KarlZeilhofer/htl-loetregler-mini/3d/batterie-adapter/bosch-hobby-18v/images/1d0ade216039de442b552e4a9faad1e7_preview_featured.JPG

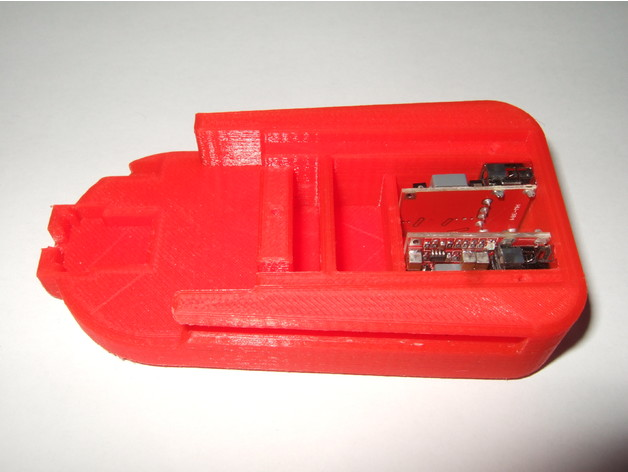
3d/batterie-adapter/bosch-hobby-18v/images/1d0ade216039de442b552e4a9faad1e7_preview_featured.JPG
