KarlZeilhofer/htl-loetregler-mini/3d/batterie-adapter/bosch-hobby-18v/images/18e0baede5127a3ce2cf0de32edce1c3_preview_featured.jpg

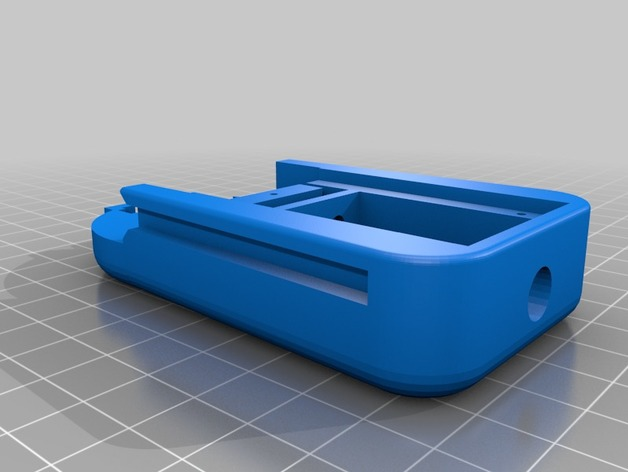
3d/batterie-adapter/bosch-hobby-18v/images/18e0baede5127a3ce2cf0de32edce1c3_preview_featured.jpg
