KarlZeilhofer/htl-loetregler-mini/3d/batterie-adapter/bosch-hobby-18v/images/176e3c1223d7b4e42e6c2fdfab14404a_preview_featured.JPG

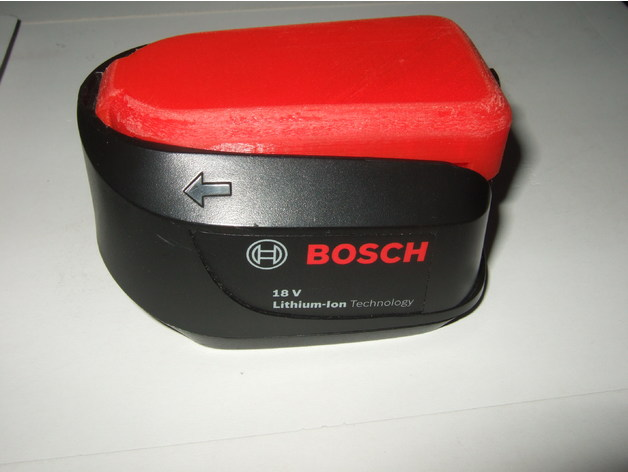
3d/batterie-adapter/bosch-hobby-18v/images/176e3c1223d7b4e42e6c2fdfab14404a_preview_featured.JPG
