KarlZeilhofer/htl-loetregler-mini/3d/batterie-adapter/bosch-hobby-18v/images/217fe692acae399ae9cad3a89807bee1_preview_featured.JPG

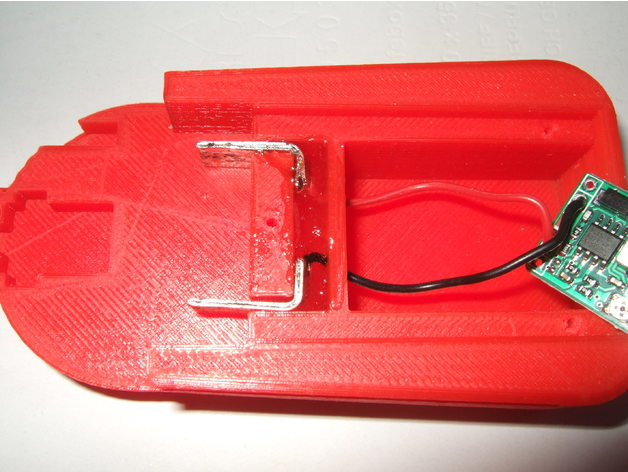
3d/batterie-adapter/bosch-hobby-18v/images/217fe692acae399ae9cad3a89807bee1_preview_featured.JPG
