KarlZeilhofer/htl-loetregler-mini/3d/batterie-adapter/bosch-hobby-18v/images/428f00f09416d94f13bab7031078e59d_preview_featured.JPG

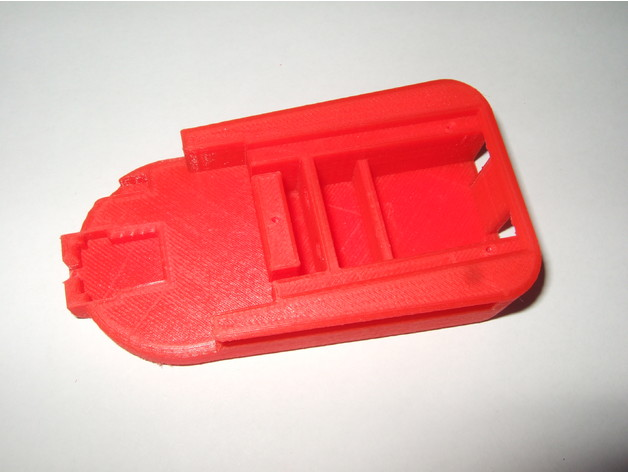
3d/batterie-adapter/bosch-hobby-18v/images/428f00f09416d94f13bab7031078e59d_preview_featured.JPG
