KarlZeilhofer/htl-loetregler-mini/3d/batterie-adapter/bosch-hobby-18v/images/aad29fb0102c40d275100bae19a4c0d0_preview_featured.JPG

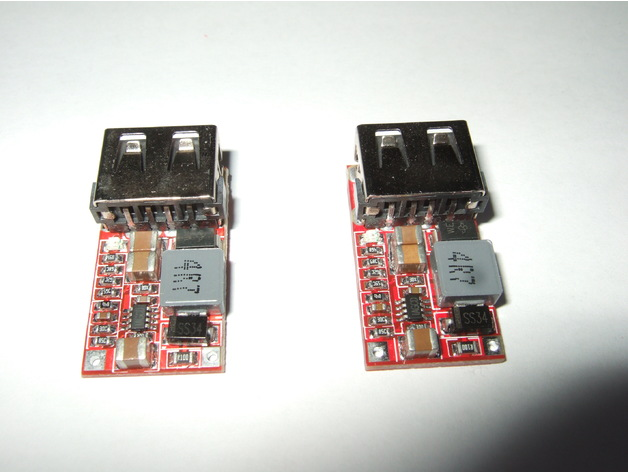
3d/batterie-adapter/bosch-hobby-18v/images/aad29fb0102c40d275100bae19a4c0d0_preview_featured.JPG
