KarlZeilhofer/htl-loetregler-mini/3d/batterie-adapter/bosch-hobby-18v/images/c5ce1f0b2175b3c10ee5914f01ce9187_preview_featured.JPG

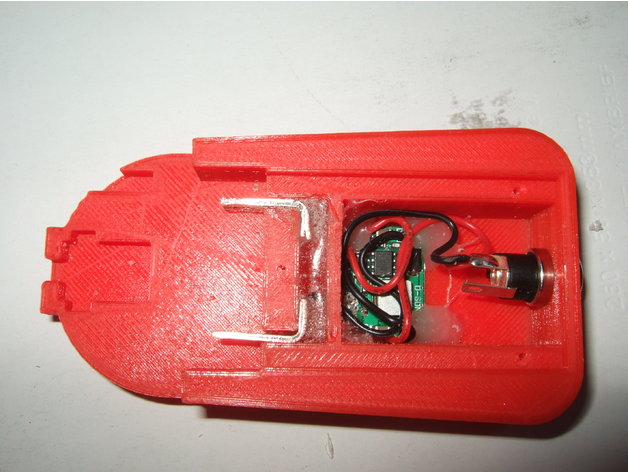
3d/batterie-adapter/bosch-hobby-18v/images/c5ce1f0b2175b3c10ee5914f01ce9187_preview_featured.JPG
