KarlZeilhofer/htl-loetregler-mini/3d/batterie-adapter/einhell/2022-06-26_001.png

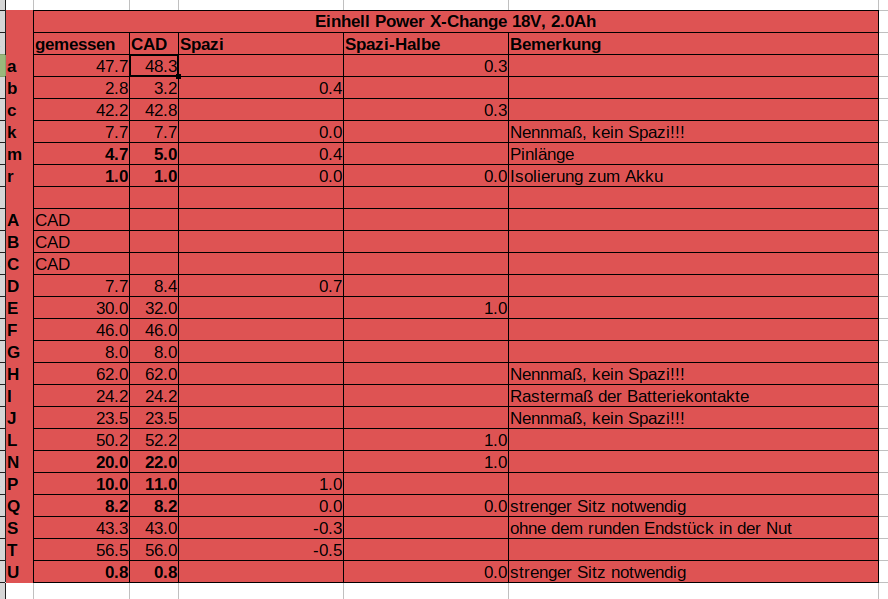
3d/batterie-adapter/einhell/2022-06-26_001.png
