KarlZeilhofer/htl-loetregler-mini/3d/batterie-adapter/einhell/skizze-aufriss.jpg

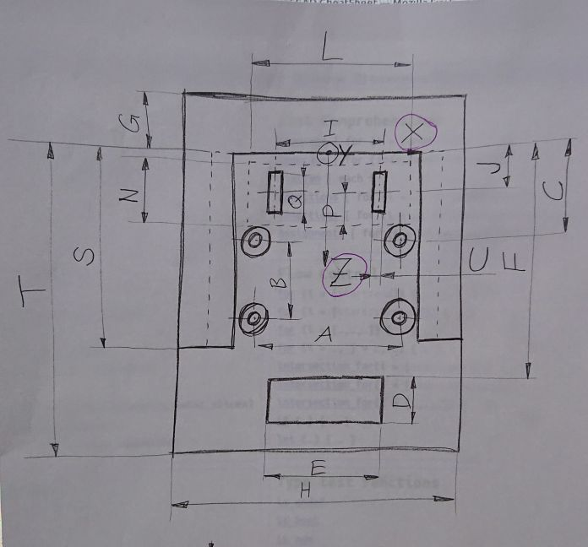
3d/batterie-adapter/einhell/skizze-aufriss.jpg
