KarlZeilhofer/htl-loetregler-mini/3d/batterie-adapter/einhell/skizze-grundriss.jpg

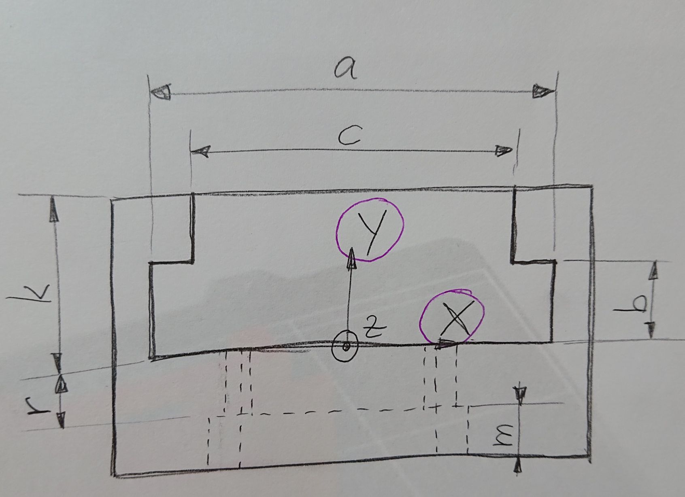
3d/batterie-adapter/einhell/skizze-grundriss.jpg
