KarlZeilhofer/htl-loetregler-mini/3d/batterie-adapter/lux-tools-1.5ah/LUX Tools 20V-1.5Ah.jpg

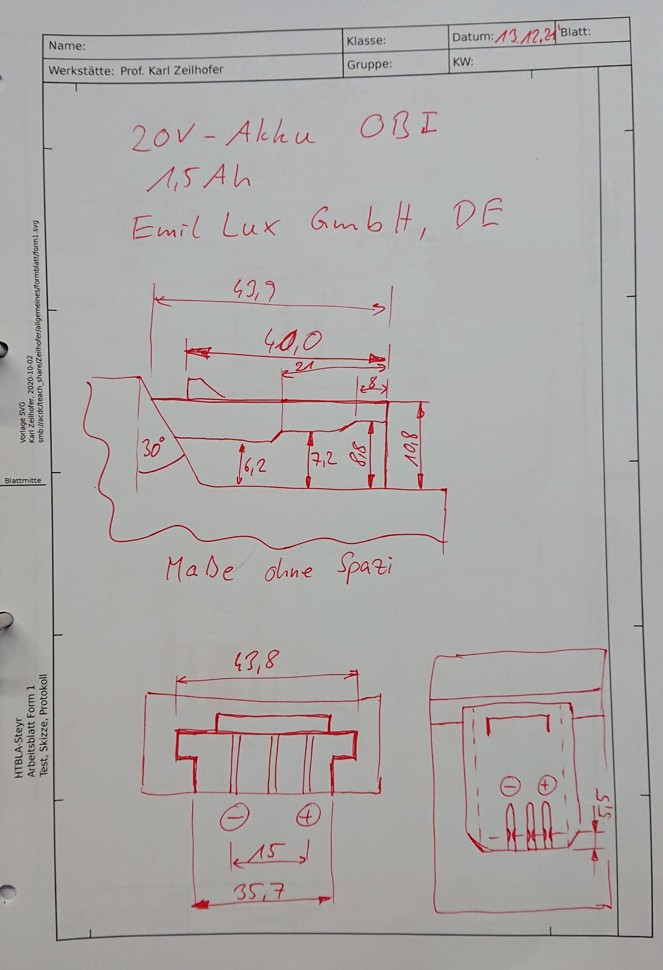
3d/batterie-adapter/lux-tools-1.5ah/LUX Tools 20V-1.5Ah.jpg
