KarlZeilhofer/htl-loetregler-mini/3d/batterie-adapter/lux-tools-2ah/LUX Tools 20V-2Ah.jpg

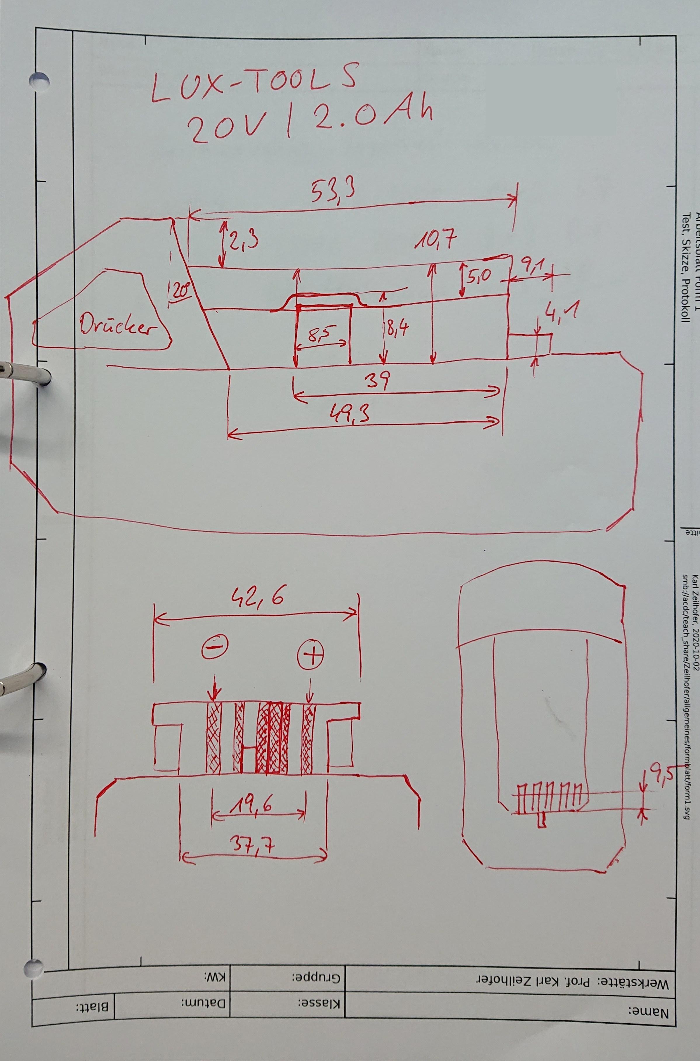
3d/batterie-adapter/lux-tools-2ah/LUX Tools 20V-2Ah.jpg
