KarlZeilhofer/htl-loetregler-mini/3d/griffstük/screenshot griffstück v1.png

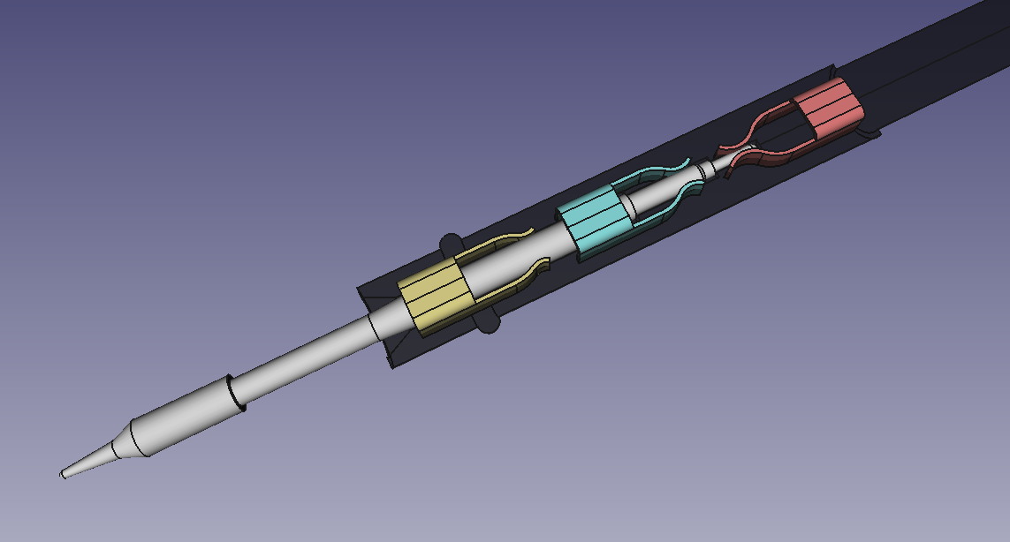
3d/griffstük/screenshot griffstück v1.png
