KarlZeilhofer/htl-loetregler-mini/berechnungen/spannungen_leistungen_spitzentypen.png

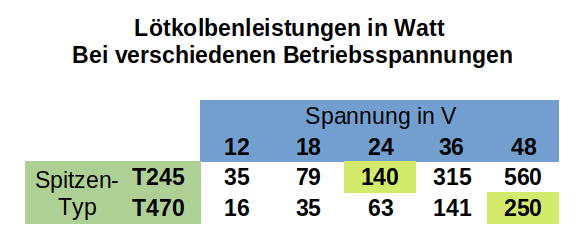
berechnungen/spannungen_leistungen_spitzentypen.png
