KarlZeilhofer/htl-loetregler-mini/kicad/cam/untitled.png

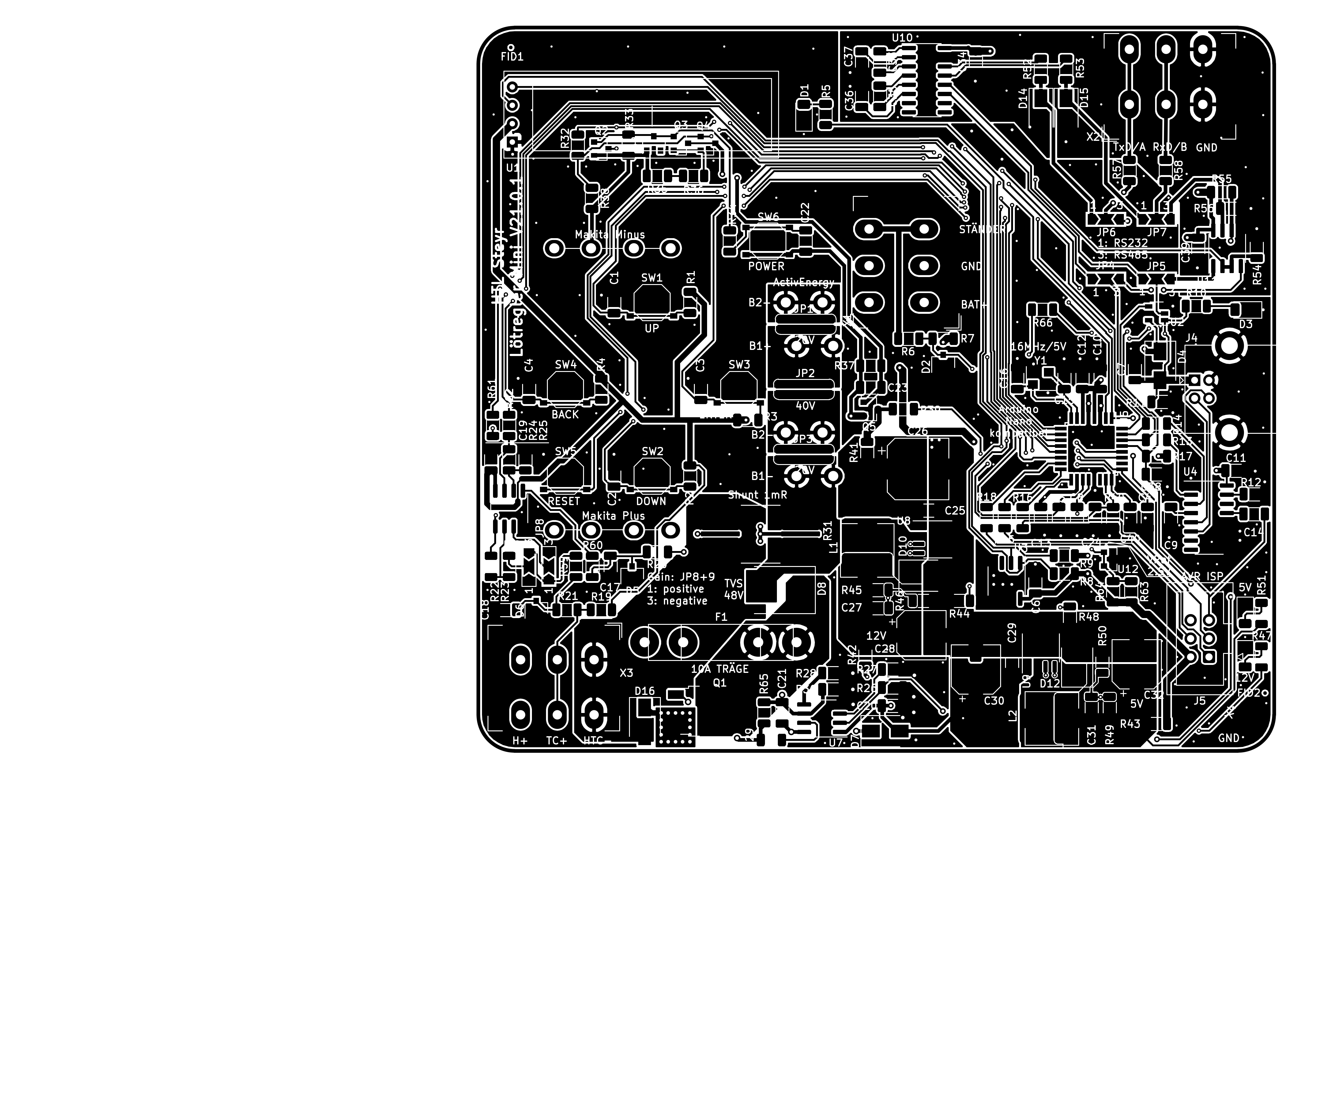
kicad/cam/untitled.png
