KarlZeilhofer/htl-loetregler-mini/3d/batterie-adapter/lux-tools-1.5ah/LUX Tools 20V-1.5Ah, Deckel v1.stl

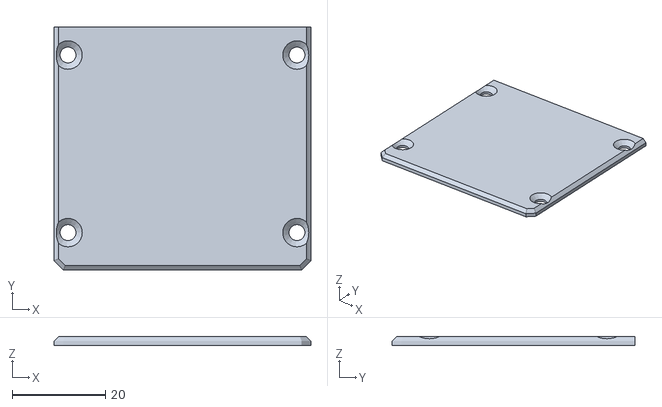
[picture p37: CAD file, 2022-02-06]
3d/batterie-adapter/lux-tools-1.5ah/LUX Tools 20V-1.5Ah, Deckel v1.stl
55.0 x 52.0 x 2.00
