KarlZeilhofer/htl-loetregler-mini/3d/batterie-adapter/milwaukee/milwaukee-batterieschuh_v2.stl

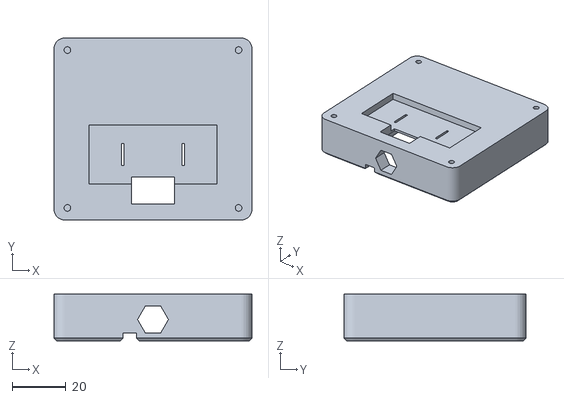
[picture p38: CAD file, 2022-06-27]
3d/batterie-adapter/milwaukee/milwaukee-batterieschuh_v2.stl
74.0 x 68.0 x 17.5
