KarlZeilhofer/htl-loetregler-mini/3d/griffstük/fingerkuppenring_v2.3.stl

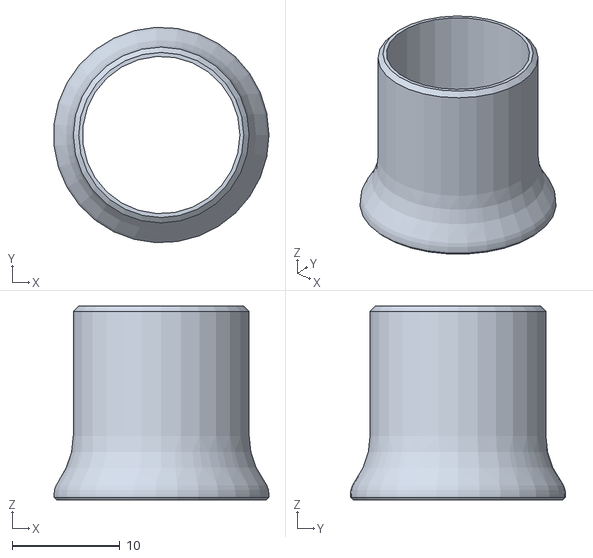
[picture p39: CAD file, 2022-06-27]
3d/griffstük/fingerkuppenring_v2.3.stl
19.9 x 20.0 x 18.0
