KarlZeilhofer/htl-loetregler-mini/3d/tiefziehform/tiefziehform_A_matrizze_v3.stl

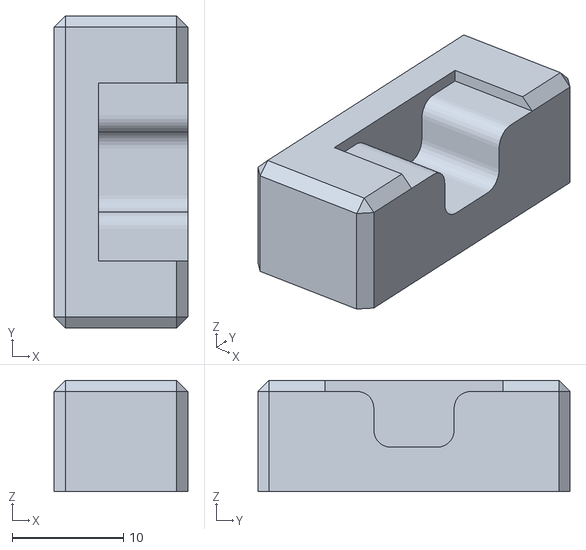
[picture p40: CAD file, 2021-06-21]
3d/tiefziehform/tiefziehform_A_matrizze_v3.stl
12.0 x 28.0 x 10.0
