KarlZeilhofer/htl-loetregler-mini/3d/batterie-adapter/berner-18v/berner-batterieschuh.FCStd

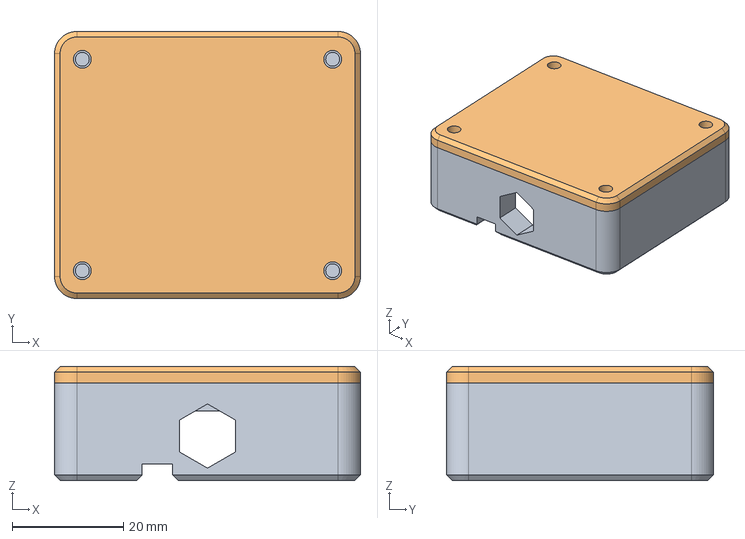
[picture p41: CAD file, 2021-11-27]
3d/batterie-adapter/berner-18v/berner-batterieschuh.FCStd
55.0 x 48.0 x 20.5 mm
Berner-18V
Deckel
