KarlZeilhofer/htl-loetregler-mini/3d/batterie-adapter/bosch-hobby-18v/files/deckel.stl

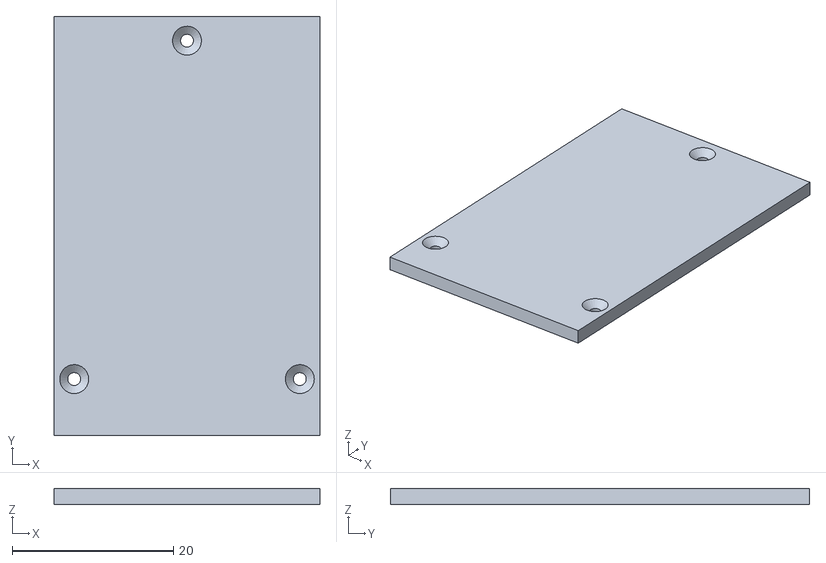
[picture p42: CAD file, 2022-02-07]
3d/batterie-adapter/bosch-hobby-18v/files/deckel.stl
33.0 x 52.0 x 2.00
