KarlZeilhofer/htl-loetregler-mini/3d/batterie-adapter/bosch-professional-18v/bosch-professional-batterieschuh_deckel_v1.stl

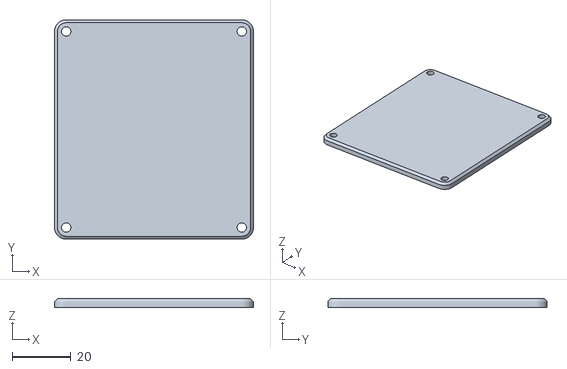
[picture p43: CAD file, 2022-06-01]
3d/batterie-adapter/bosch-professional-18v/bosch-professional-batterieschuh_deckel_v1.stl
68.0 x 75.0 x 3.00
