KarlZeilhofer/htl-loetregler-mini/3d/batterie-adapter/lux-tools-1.5ah/LUX Tools 20V-1.5Ah, Schuh v1.stl

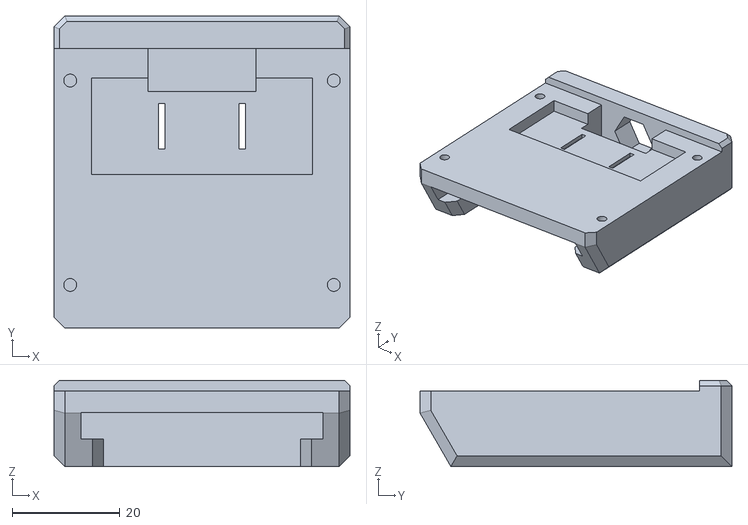
[picture p44: CAD file, 2022-02-06]
3d/batterie-adapter/lux-tools-1.5ah/LUX Tools 20V-1.5Ah, Schuh v1.stl
55.0 x 58.0 x 16.0
