KarlZeilhofer/htl-loetregler-mini/3d/batterie-adapter/lux-tools-2ah/lux-tools-2Ah_batterieschuh_deckel_v2.stl

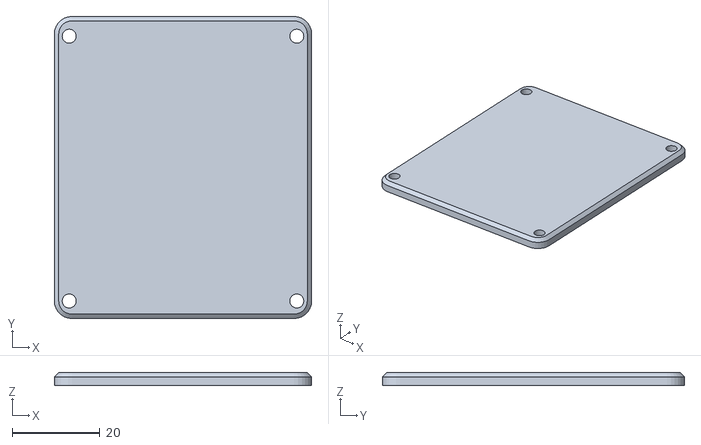
[picture p45: CAD file, 2022-06-27]
3d/batterie-adapter/lux-tools-2ah/lux-tools-2Ah_batterieschuh_deckel_v2.stl
58.8 x 69.0 x 3.00
