KarlZeilhofer/htl-loetregler-mini/3d/gehäuse/lötregler-gehäuse.FCStd

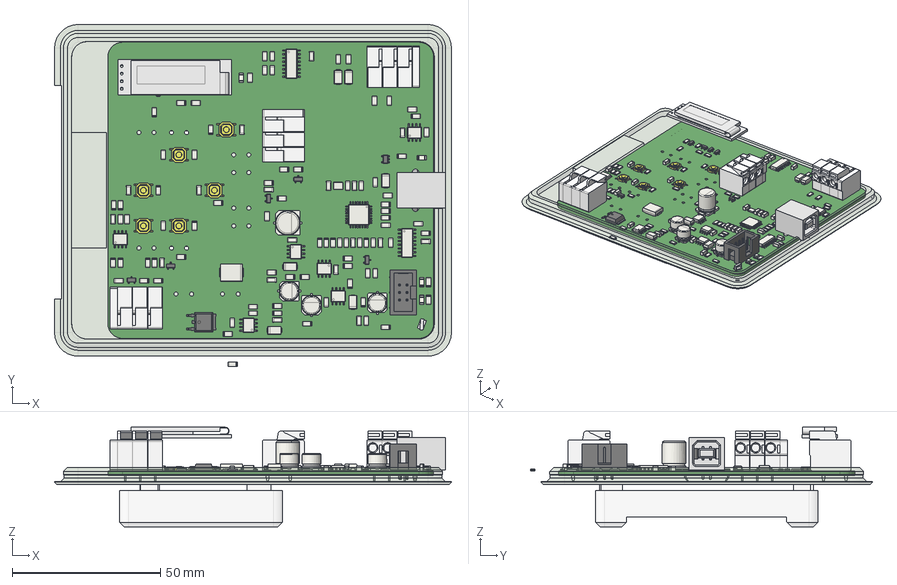
[picture p46: CAD file, 2022-06-27]
3d/gehäuse/lötregler-gehäuse.FCStd
134.0 x 115.5 x 33.6 mm
Boden_Makita_v4
Makita_Schuh
