KarlZeilhofer/htl-loetregler-mini/3d/griffstük/griffstück_v2.FCStd

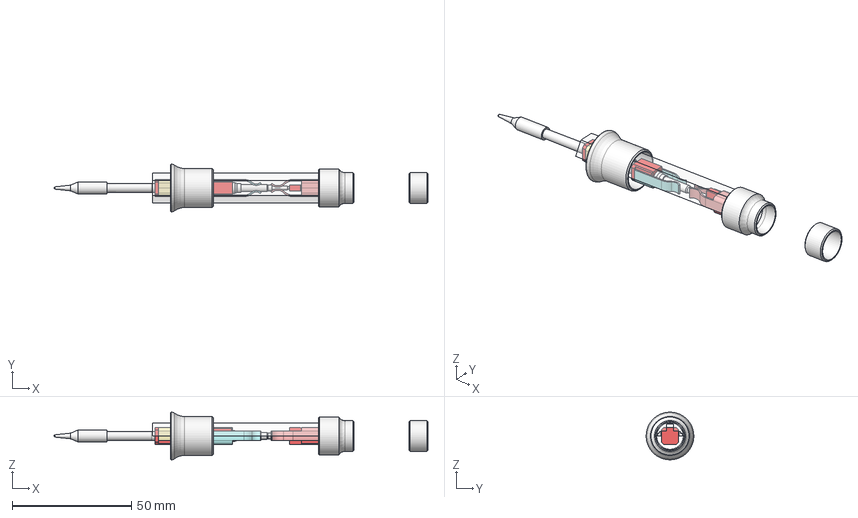
[picture p47: CAD file, 2022-06-27]
3d/griffstük/griffstück_v2.FCStd
156.8 x 20.0 x 20.0 mm
JBC-2245-003
Federkontakt_HTC-
Federkontakt_H+
Federkontakt_TC+
Fingerkuppenring_v2.1
Mittenring_v2
Endring_v2
Isolator_H+
Isolator_HTC-
Isolator_TC+
Halbschale-hex1
