KarlZeilhofer/htl-loetregler-mini/3d/batterie-adapter/berner-18v/berner-18v.3mf

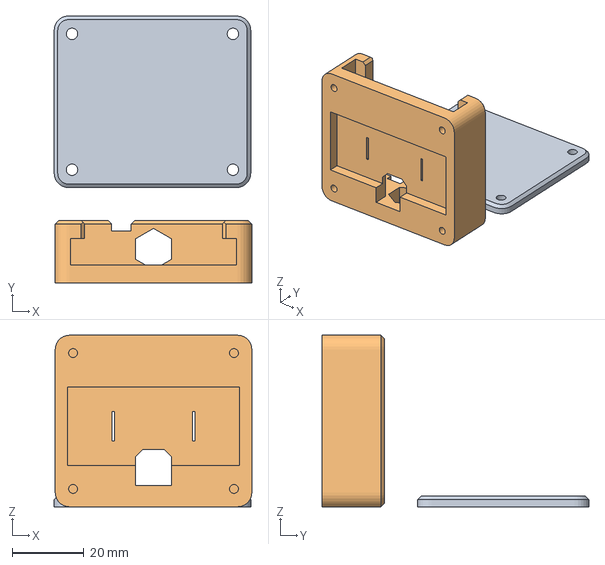
[picture p48: CAD file, 2021-11-27]
3d/batterie-adapter/berner-18v/berner-18v.3mf
55.3 x 74.7 x 48.0 mm
berner-18v_deckel.stl
berner-18v_hauptteil.stl
