KarlZeilhofer/htl-loetregler-mini/3d/batterie-adapter/einhell/einhell-batterieschuh_deckel_v1.stl

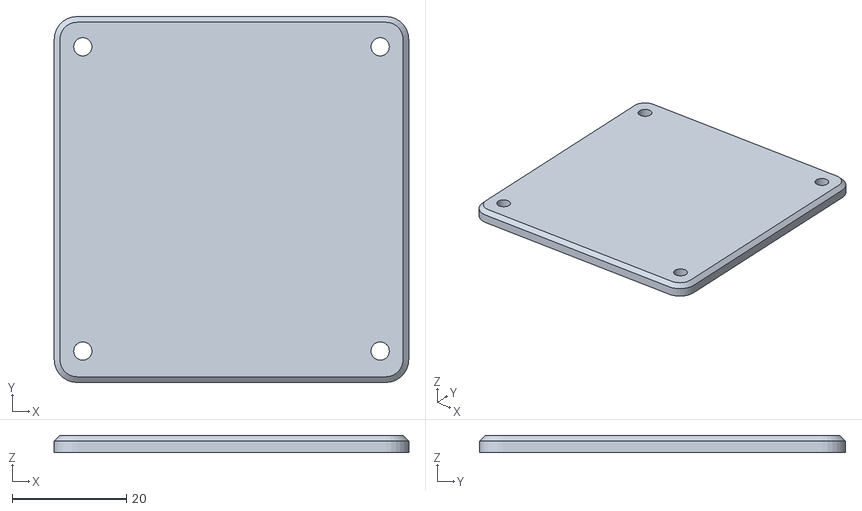
[picture p49: CAD file, 2022-06-27]
3d/batterie-adapter/einhell/einhell-batterieschuh_deckel_v1.stl
62.0 x 64.0 x 3.00
