KarlZeilhofer/htl-loetregler-mini/3d/batterie-adapter/makita/Makita_Schuh_v3.stl

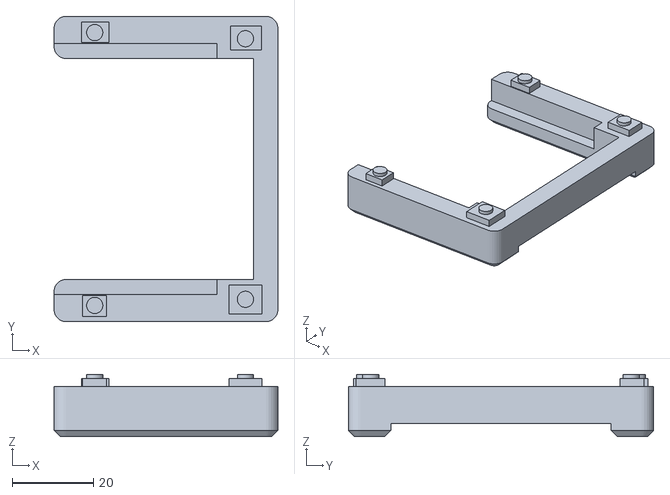
[picture p50: CAD file, 2022-02-07]
3d/batterie-adapter/makita/Makita_Schuh_v3.stl
55.0 x 75.0 x 15.2
