KarlZeilhofer/htl-loetregler-mini/3d/batterie-adapter/milwaukee/milwaukee-batterieschuh_deckel_v1.stl

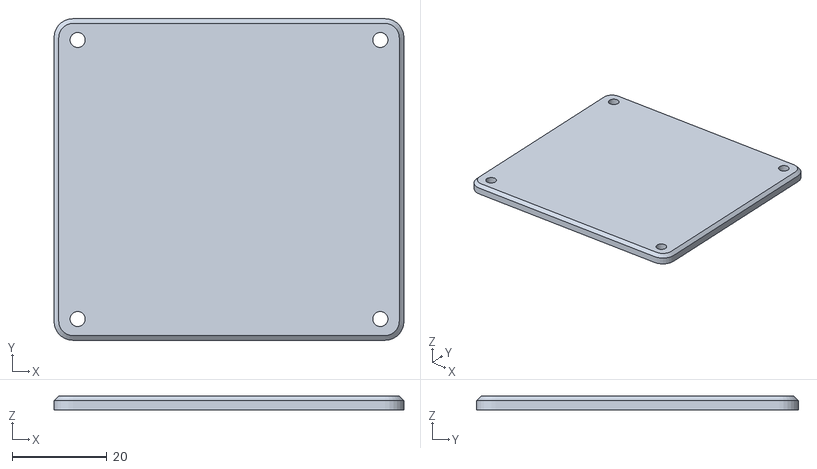
[picture p51: CAD file, 2022-06-27]
3d/batterie-adapter/milwaukee/milwaukee-batterieschuh_deckel_v1.stl
74.0 x 68.0 x 3.00
