KarlZeilhofer/htl-loetregler-mini/3d/gehäuse/zugentlastung_v1.3.3mf

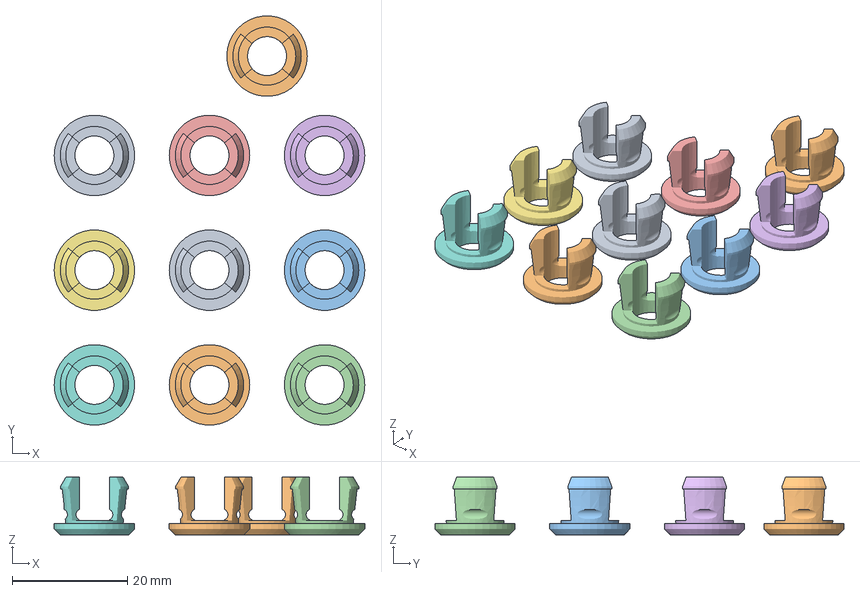
[picture p52: CAD file, 2022-06-01]
3d/gehäuse/zugentlastung_v1.3.3mf
54.0 x 71.1 x 10.0 mm
