KarlZeilhofer/htl-loetregler-mini/3d/griffstük/griffstück_isolatoren_v2.2 Polycarbonat.3mf

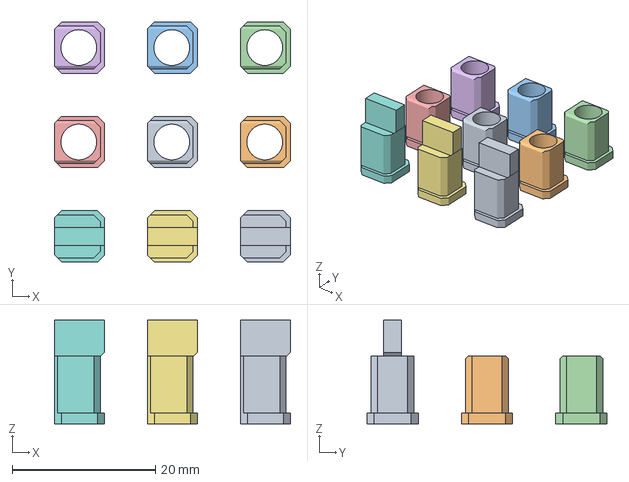
[picture p53: CAD file, 2022-06-01]
3d/griffstük/griffstück_isolatoren_v2.2 Polycarbonat.3mf
33.0 x 33.6 x 14.5 mm
griffstück_isolator_htc-_h+_v2.2.stl
griffstück_isolator_tc+.stl
