KarlZeilhofer/htl-loetregler-mini/3d/tiefziehform/tiefziehform.FCStd

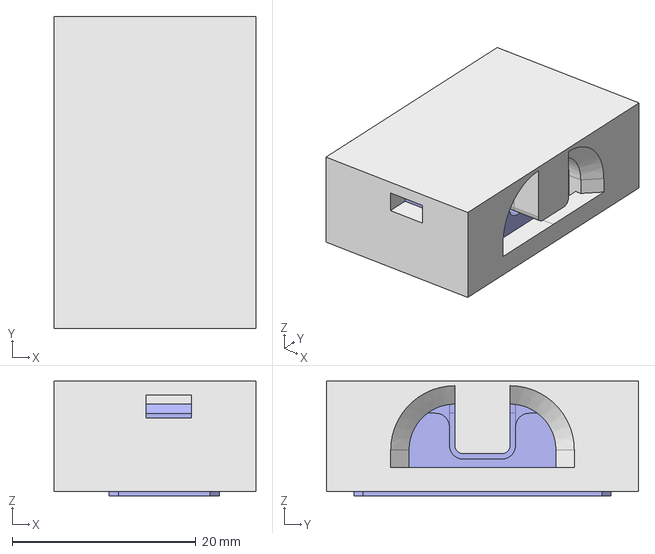
[picture p54: CAD file, 2021-06-21]
3d/tiefziehform/tiefziehform.FCStd
22.0 x 34.0 x 12.5 mm
U-Form_matrizze
U-Form_stempel
