KarlZeilhofer/htl-loetregler-mini/3d/gehäuse/blindstopfen.FCStd

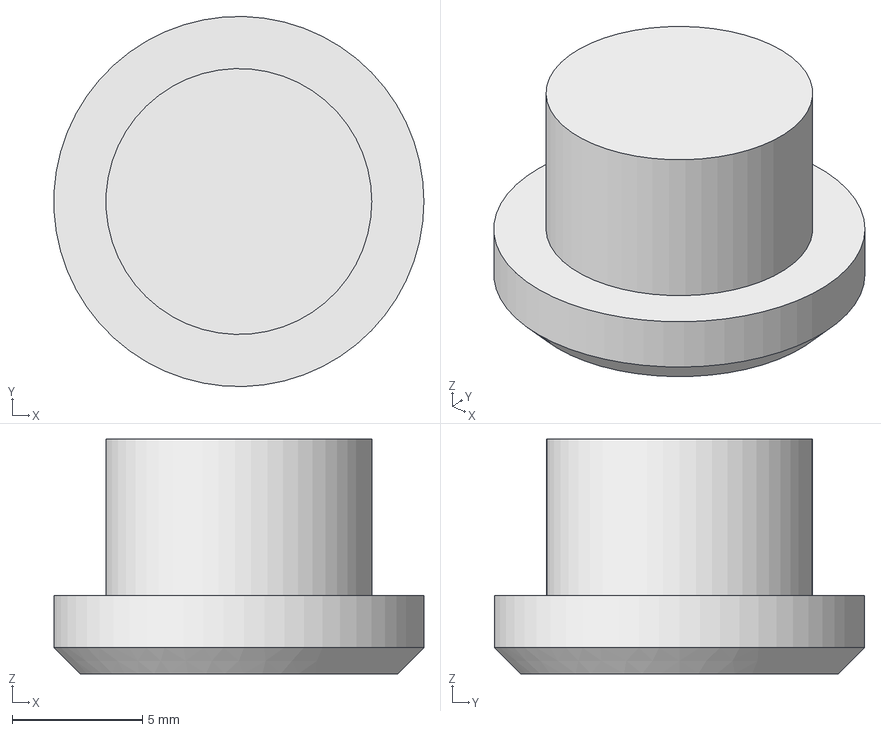
[picture p55: CAD file, 2022-06-01]
3d/gehäuse/blindstopfen.FCStd
14.2 x 14.2 x 9.00 mm
