KarlZeilhofer/htl-loetregler-mini/3d/griffstük/griffstück_halbschale-hex_v2_Polycarbonat.3mf

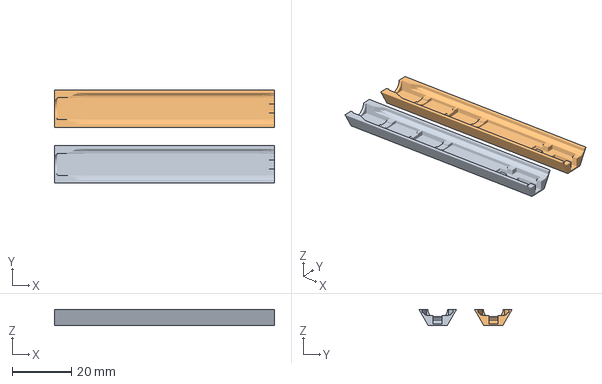
[picture p56: CAD file, 2022-06-01]
3d/griffstük/griffstück_halbschale-hex_v2_Polycarbonat.3mf
74.0 x 31.4 x 5.50 mm
