KarlZeilhofer/htl-loetregler-mini/3d/gehäuse/blindstopfen_v1.3mf

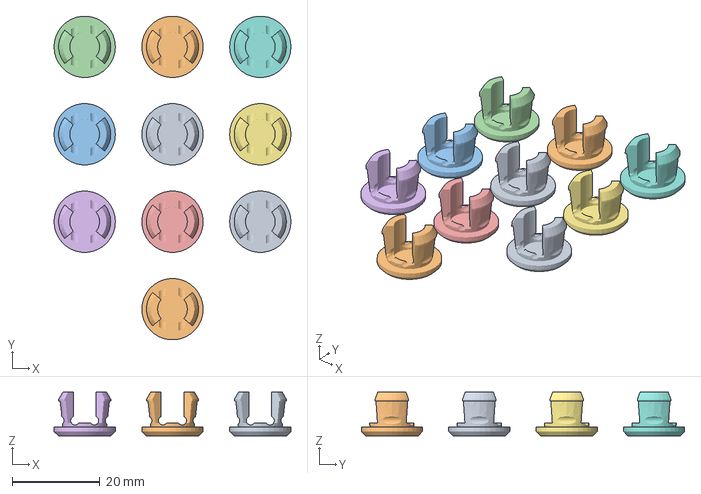
[picture p57: CAD file, 2021-11-27]
3d/gehäuse/blindstopfen_v1.3mf
54.1 x 73.8 x 10.0 mm
