KarlZeilhofer/htl-loetregler-mini/3d/griffstük/griffstück_isolatoren_v2.2 (perfektes ergebnis).3mf

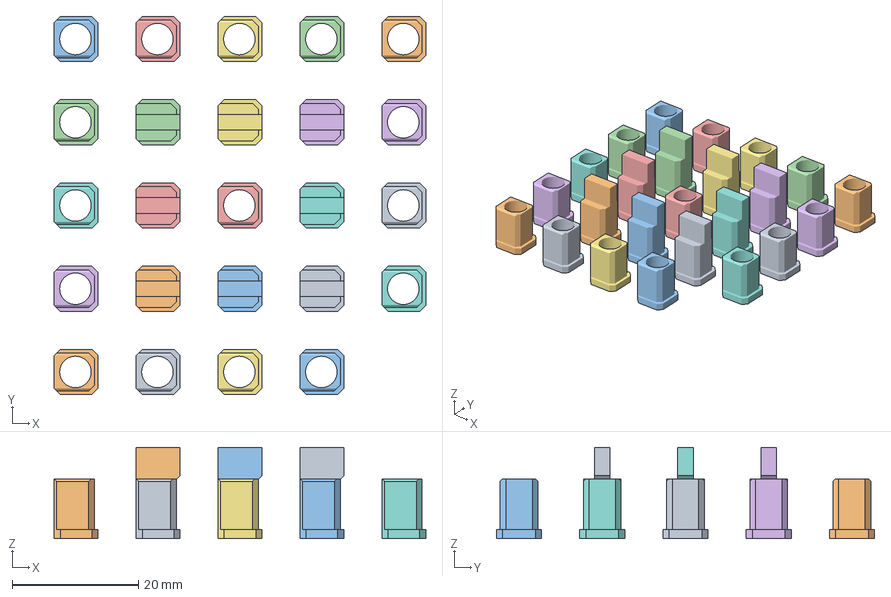
[picture p58: CAD file, 2022-04-04]
3d/griffstük/griffstück_isolatoren_v2.2 (perfektes ergebnis).3mf
59.0 x 60.0 x 14.5 mm
griffstück_isolator_htc-_h+_v2.2.stl
griffstück_isolator_tc+.stl
