KarlZeilhofer/htl-loetregler-mini/3d/griffstük/griffstück_isolator_htc-_h+_v2.2.stl

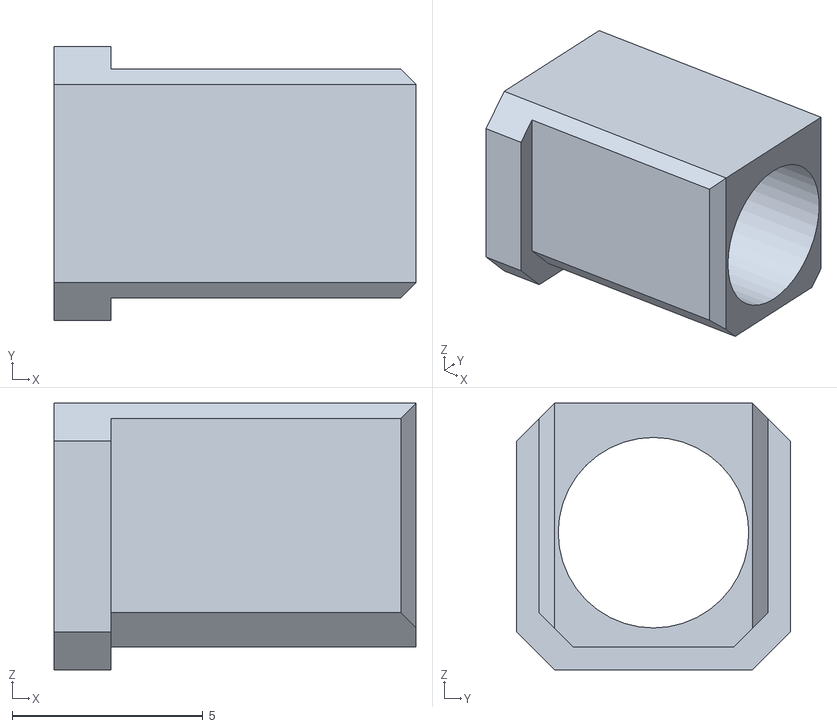
[picture p60: CAD file, 2021-11-29]
3d/griffstük/griffstück_isolator_htc-_h+_v2.2.stl
9.50 x 7.20 x 7.00
