KarlZeilhofer/htl-loetregler-mini/3d/gehäuse/lötregler-gehäuse-deckel_v2.stl

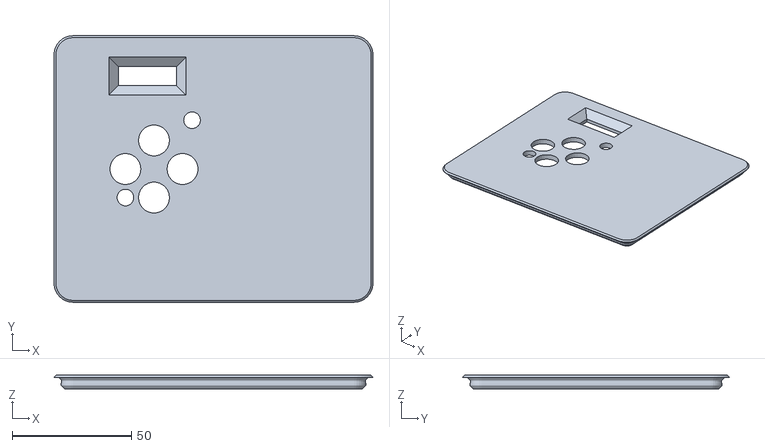
[picture p61: CAD file, 2021-11-27]
3d/gehäuse/lötregler-gehäuse-deckel_v2.stl
134.0 x 112.0 x 5.80
