KarlZeilhofer/htl-loetregler-mini/3d/griffstük/endring_v2.1.stl

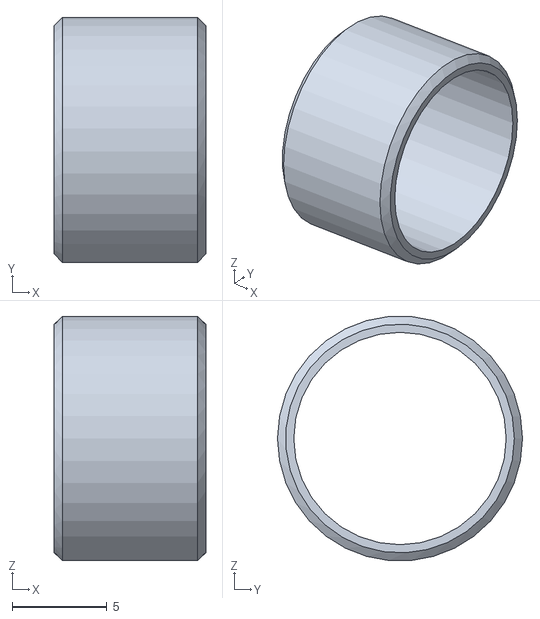
[picture p62: CAD file, 2021-11-27]
3d/griffstük/endring_v2.1.stl
8.00 x 12.9 x 12.9
