KarlZeilhofer/htl-loetregler-mini/3d/gehäuse/lötregler-gehäuse-wand_v2.3mf

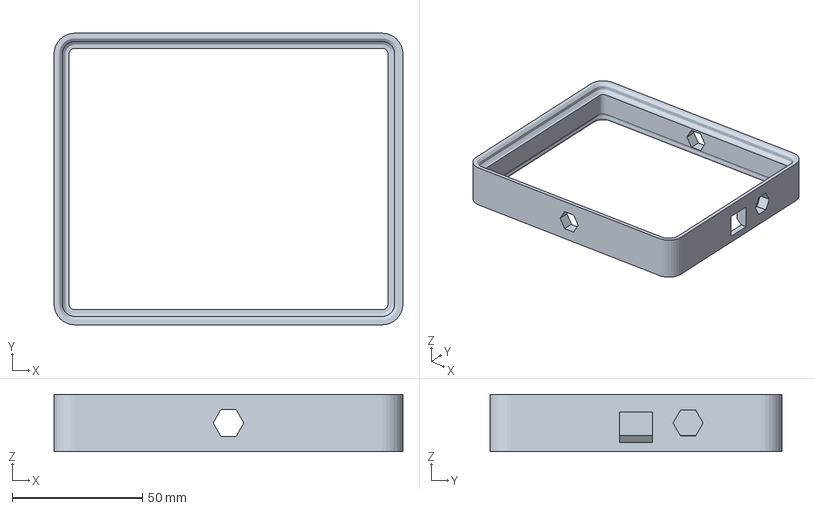
[picture p63: CAD file, 2021-07-06]
3d/gehäuse/lötregler-gehäuse-wand_v2.3mf
134.0 x 112.0 x 22.0 mm
