KarlZeilhofer/htl-loetregler-mini/3d/griffstük/mittenring_v2.1.stl

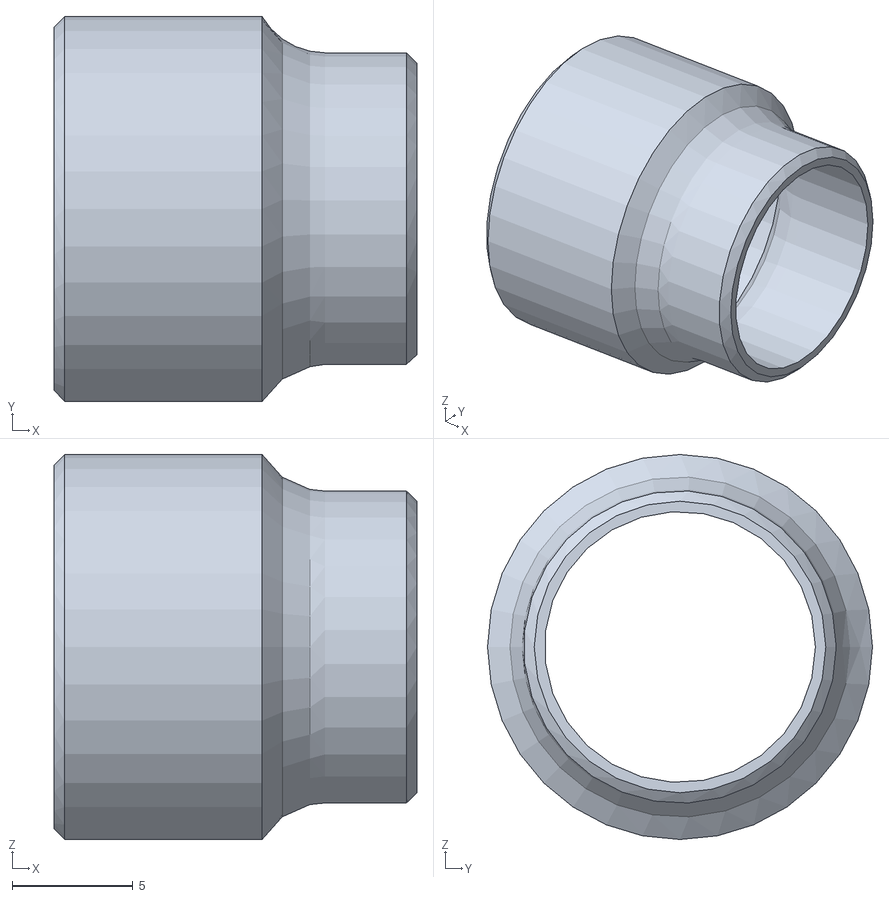
[picture p64: CAD file, 2021-11-27]
3d/griffstük/mittenring_v2.1.stl
15.0 x 15.9 x 15.9
