KarlZeilhofer/htl-loetregler-mini/3d/gehäuse/taster_v2.stl

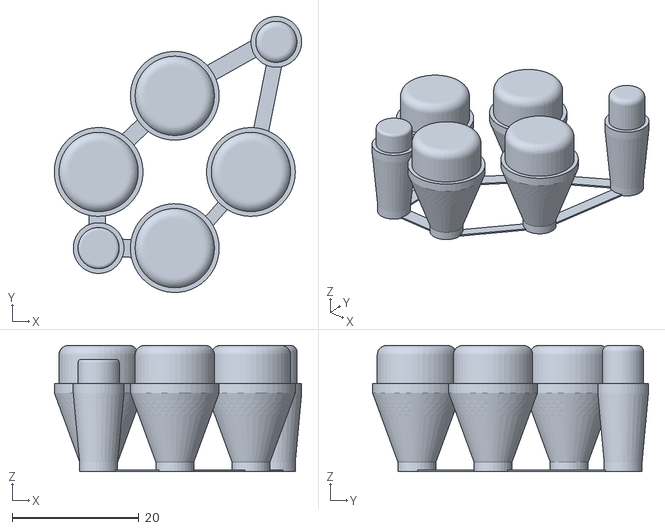
[picture p65: CAD file, 2021-07-05]
3d/gehäuse/taster_v2.stl
39.0 x 43.5 x 19.9
