KarlZeilhofer/htl-loetregler-mini/3d/gehäuse/lötregler-gehäuse-deckel+wand_v1.3mf

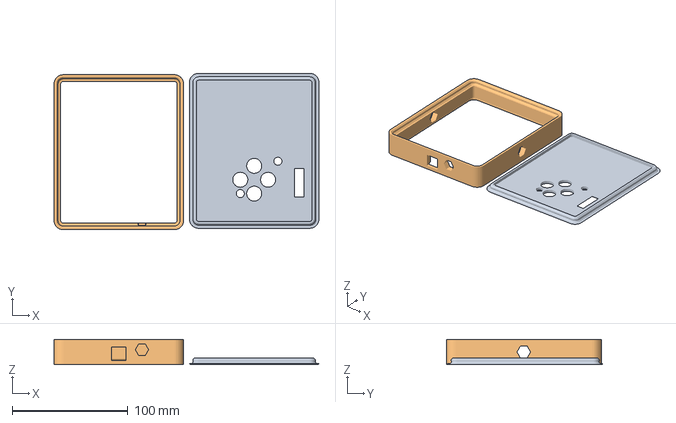
[picture p66: CAD file, 2021-07-01]
3d/gehäuse/lötregler-gehäuse-deckel+wand_v1.3mf
229.0 x 135.2 x 22.0 mm
lötregler-gehäuse-deckel_v1.stl
lötregler-gehäuse-wand_v1.stl
