KarlZeilhofer/htl-loetregler-mini/3d/griffstük/griffstück_halbschale-rund_v2.stl

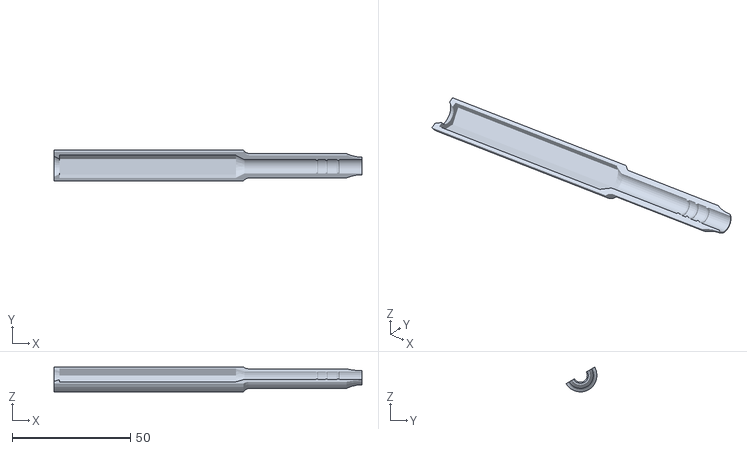
[picture p67: CAD file, 2021-11-27]
3d/griffstük/griffstück_halbschale-rund_v2.stl
130.0 x 13.1 x 10.5
