KarlZeilhofer/htl-loetregler-mini/3d/griffstük/griffstück_halbschale-hex_v2.stl

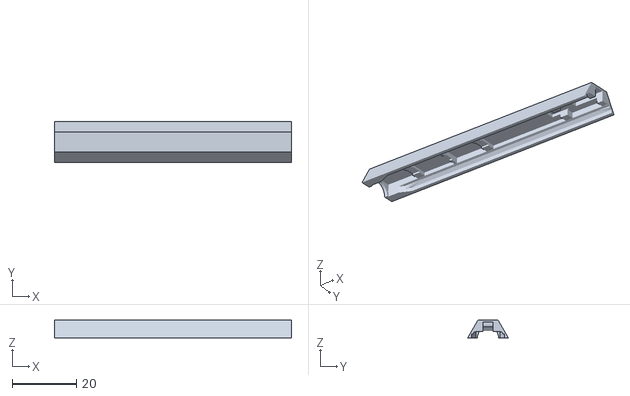
[picture p68: CAD file, 2021-11-27]
3d/griffstük/griffstück_halbschale-hex_v2.stl
74.0 x 12.7 x 5.50
