KarlZeilhofer/htl-loetregler-mini/3d/griffstük/griffstück_isolator_tc+.stl

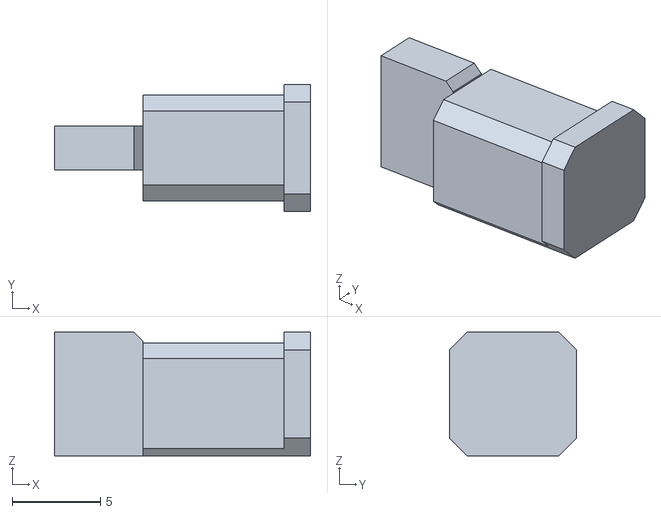
[picture p69: CAD file, 2021-11-27]
3d/griffstük/griffstück_isolator_tc+.stl
14.5 x 7.20 x 7.00
