KarlZeilhofer/htl-loetregler-mini/3d/griffstük/griffstück_unten_v0.0.4.stl

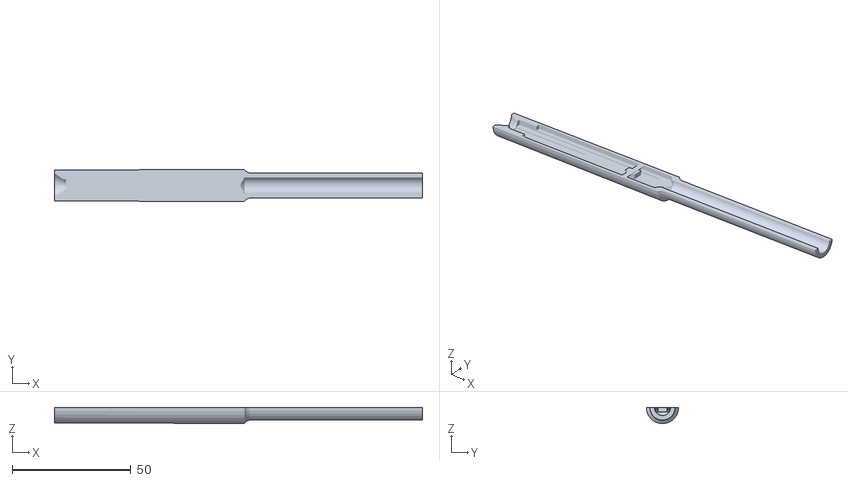
[picture p70: CAD file, 2021-11-27]
3d/griffstük/griffstück_unten_v0.0.4.stl
155.0 x 13.6 x 6.75
