KarlZeilhofer/htl-loetregler-mini/3d/griffstük/griffstück_unten_v0.0.1.3mf

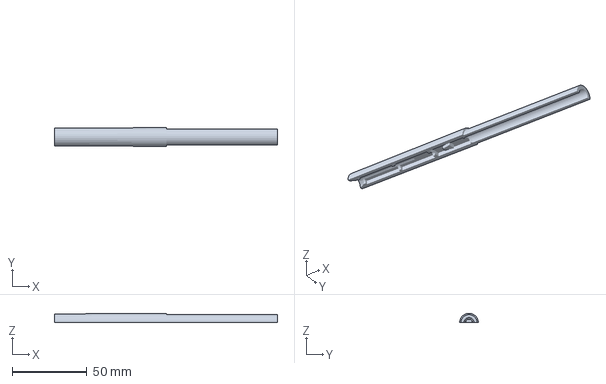
[picture p71: CAD file, 2021-06-21]
3d/griffstük/griffstück_unten_v0.0.1.3mf
149.0 x 12.6 x 6.25 mm
