KarlZeilhofer/htl-loetregler-mini/3d/griffstük/griffstück_oben_v0.0.3.stl

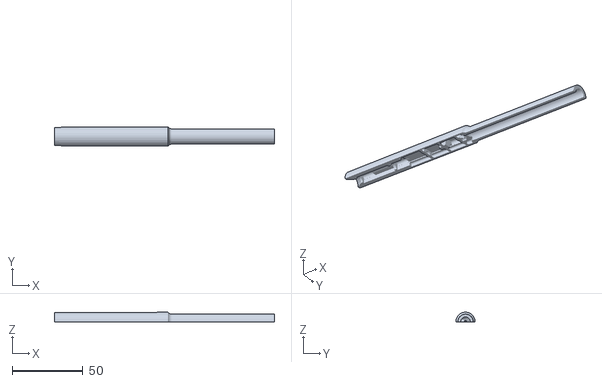
[picture p72: CAD file, 2021-06-21]
3d/griffstük/griffstück_oben_v0.0.3.stl
155.0 x 13.6 x 6.75
