KarlZeilhofer/htl-loetregler-mini/3d/griffstük/griffstück_oben_v0.0.1.3mf

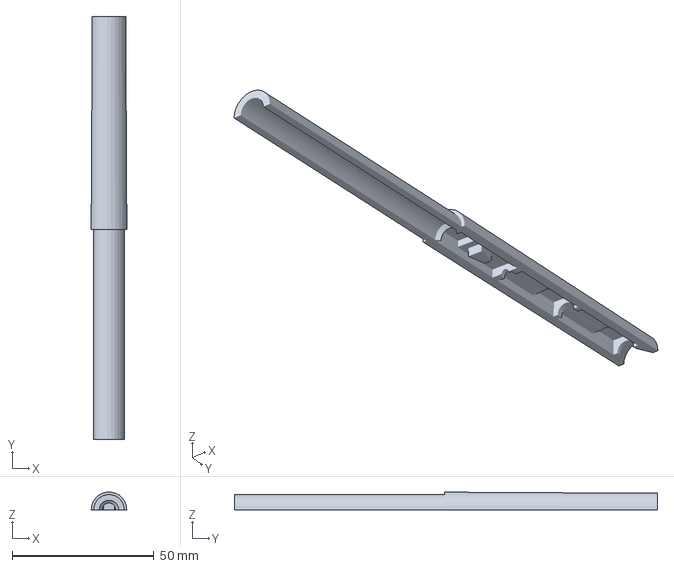
[picture p73: CAD file, 2021-06-21]
3d/griffstük/griffstück_oben_v0.0.1.3mf
12.6 x 149.0 x 6.25 mm
