KarlZeilhofer/htl-loetregler-mini/3d/griffstük/federkontakt_v2.1_laser.dxf

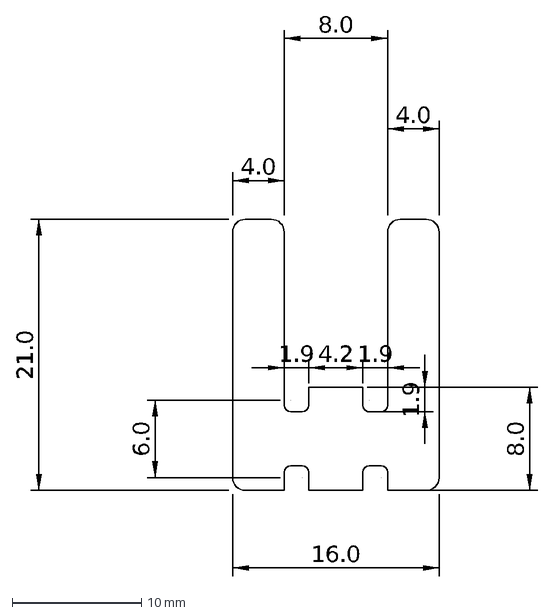
[picture p74: CAD file, 2021-06-17]
3d/griffstük/federkontakt_v2.1_laser.dxf
16.0
8.0
4.0
6.0
21.0
4.2
1.9
